TU-Darmstadt-APQ/phase-frequency_detector/spice/Draft1.asc

C1: cap; 330p
R1: res; 2.5k
R2: res; 51
R3: res; 51
R4: res; 49.9
V1: voltage; AC 1
Named nets: 0
.ac dec 10 1 50MEG
