TU-Darmstadt-APQ/phase-frequency_detector/spice/Rev1.1.asc

C1: cap; 33p
C2: cap; 33p
C3: cap; 560p
C4: cap; 140p
C5: cap; 330p
C6: cap; 560p
C7: cap; 33p
C8: cap; 1µ
R1: res; 200
R2: res; 200
R3: res; 200
R4: res; 400
R5: res; 400
R6: res; 100
R7: res; 49.9
R8: res; 200
R9: res; 49.9
R10: res; 51
R11: res; 1200
R12: res; 51
R13: res; 50
R14: res; 0
R15: res; 1.2k
R16: res; 200
R17: res; 200
R18: res; 49.9
R20: res; 50
U1: ADA4896
U2: ADA4896
U3: ADA4896
U6: ADA4896
V1: voltage; 5
V2: voltage; 5
V3: voltage; 0; AC 1
Named nets: 0, +5V, -5V
.ac dec 50 1k 100MEG
;noise V(n013) V3 dec 50 1k 100MEG
